Dima-Shlenkevitch/Tactile-On-Off-Power-Switch/Project Documentation/Step 2 - Design Phase/FreeCAD design - THT.png

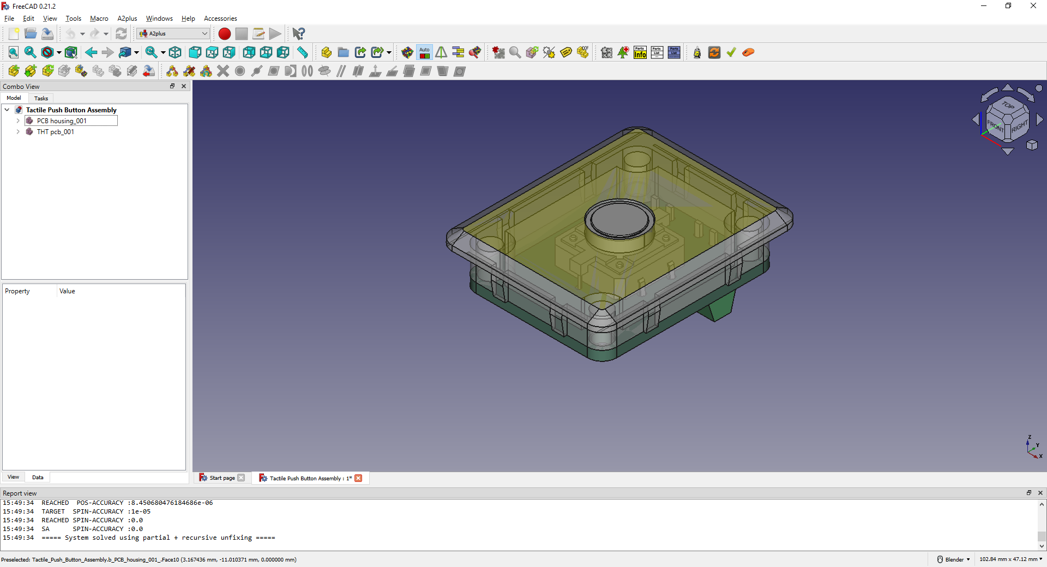
Project Documentation/Step 2 - Design Phase/FreeCAD design - THT.png
