Dima-Shlenkevitch/Tactile-On-Off-Power-Switch/Project Documentation/Step 2 - Design Phase/Mechanical Design/Tactile Switch/PCB Models/THT assembly-exploded.png

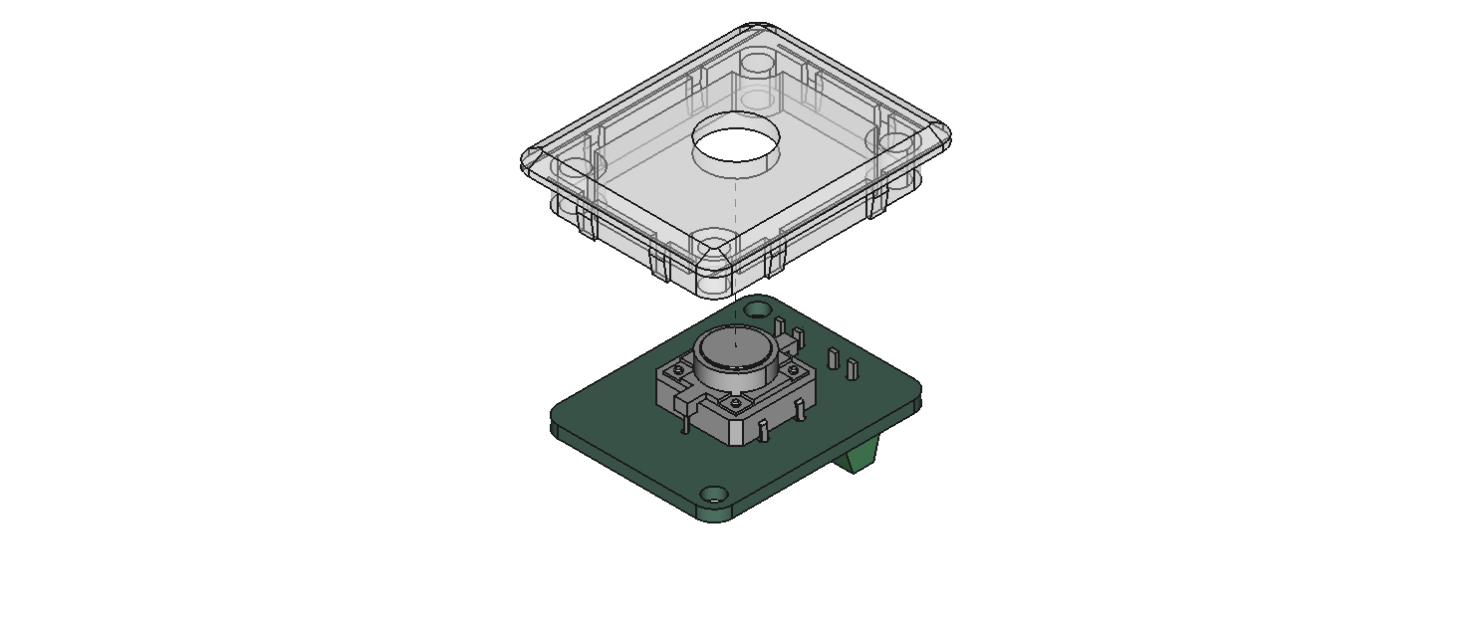
Project Documentation/Step 2 - Design Phase/Mechanical Design/Tactile Switch/PCB Models/THT assembly-exploded.png
