Dima-Shlenkevitch/Tactile-On-Off-Power-Switch/Project Documentation/Step 2 - Design Phase/Mechanical Design/Tactile Switch/PCB Models/THT assembly.png

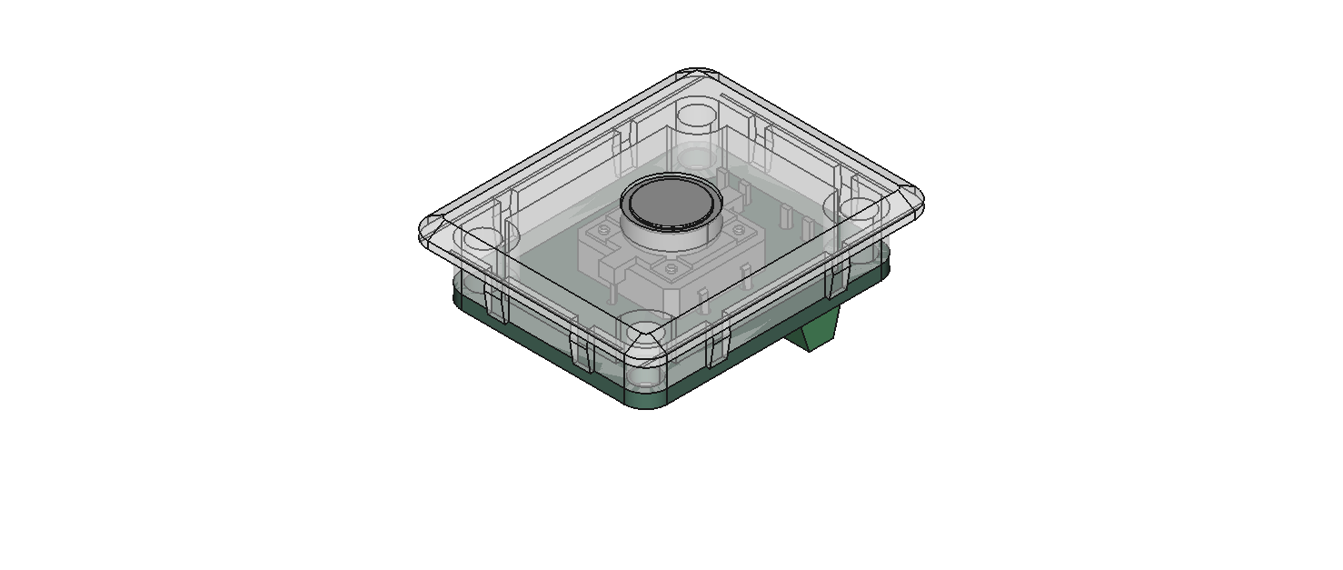
Project Documentation/Step 2 - Design Phase/Mechanical Design/Tactile Switch/PCB Models/THT assembly.png
